ricet/AirQualityMonitor/test/co2test.py

#!/usr/bin/python3

import time
import board
import adafruit_scd30

i2c = board.I2C()   # uses board.SCL and board.SDA
scd = adafruit_scd30.SCD30(i2c)

while True:
    # since the measurement interval is long (2+ seconds) we check for new data before reading
    # the values, to ensure current readings.
    if scd.data_available:
        print("Data Available!")
        print("CO2:", scd.CO2, "PPM")
        print("Temperature:", scd.temperature, "degrees C")
        print("Humidity:", scd.relative_humidity, "%%rH")
        print("")
        print("Waiting for new data...")
        print("")

    time.sleep(0.5)
